andrenho-try-new-things/fortuna-computer-base/schematic/pi-pico-vga.kicad_sch

## KiCad design schematic/pi-pico-vga.kicad_sch (2025-05-28, an earlier design)

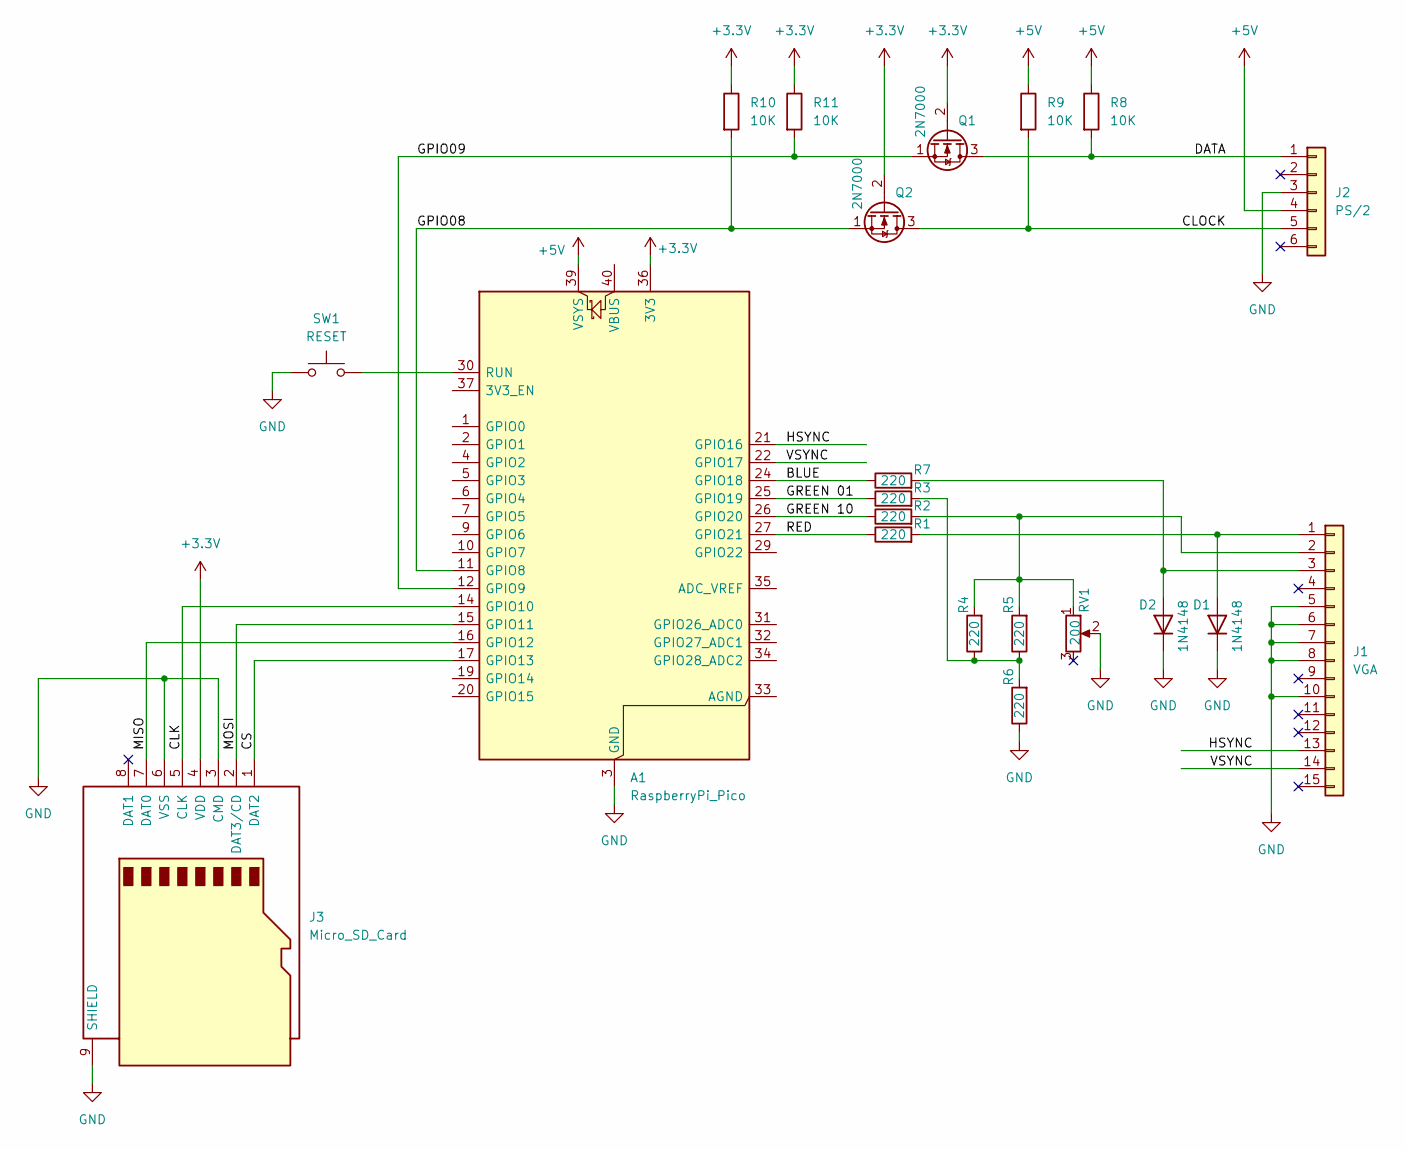
[picture p4: schematic pi-pico-vga.kicad_sch]

Parts:
A1: RaspberryPi_Pico; RaspberryPi_Pico_Common_Unspecified
D1, D2: 1N4148; D_DO-35_SOD27_P7.62mm_Horizontal
J1: VGA
J2: PS/2
J3: Micro_SD_Card
Q1, Q2: 2N7000; TO-92_Inline
R1, R2, R3, R4, R5, R6, R7: 220
R8, R9, R10, R11: 10K
RV1: 200
SW1: RESET

Connections:
+3.3V: A1.36 (3V3), J3.4 (VDD), Q1.2 (G), Q2.2 (G), R10.1, R11.1
+5V: A1.39 (VSYS), J2.4, R8.1, R9.1
BLUE: A1.24 (GPIO18), R7.1
CLK: A1.14 (GPIO10), J3.5 (CLK)
CLOCK: J2.5, Q2.3 (D), R9.2
CS: A1.17 (GPIO13), J3.1 (DAT2)
DATA: J2.1, Q1.3 (D), R8.2
GND: A1.3 (GND), A1.8 (GND), A1.13 (GND), A1.18 (GND), A1.23 (GND), A1.28 (GND), A1.38 (GND), D1.1 (K), D2.1 (K), J1.5, J1.6, J1.7, J1.8, J1.10, J2.3, J3.3 (CMD), J3.6 (VSS), J3.9 (SHIELD), R6.1, RV1.2, SW1.1
GPIO08: A1.11 (GPIO8), Q2.1 (S), R10.2
GPIO09: A1.12 (GPIO9), Q1.1 (S), R11.2
GREEN 01: A1.25 (GPIO19), R3.1
GREEN 10: A1.26 (GPIO20), R2.1
HSYNC: A1.21 (GPIO16), J1.13
MISO: A1.16 (GPIO12), J3.7 (DAT0)
MOSI: A1.15 (GPIO11), J3.2 (DAT3/CD)
unnamed: A1.30 (RUN), SW1.2
unnamed: D1.2 (A), J1.1, R1.2
unnamed: D2.2 (A), J1.3, R7.2
unnamed: J1.2, R2.2, R4.2, R5.2, RV1.1
unnamed: R3.2, R4.1, R5.1, R6.2
RED: A1.27 (GPIO21), R1.1
VSYNC: A1.22 (GPIO17), J1.14
